HasanJamal96/esp32_prayer_reminder/Code/main/data/bg.jpg

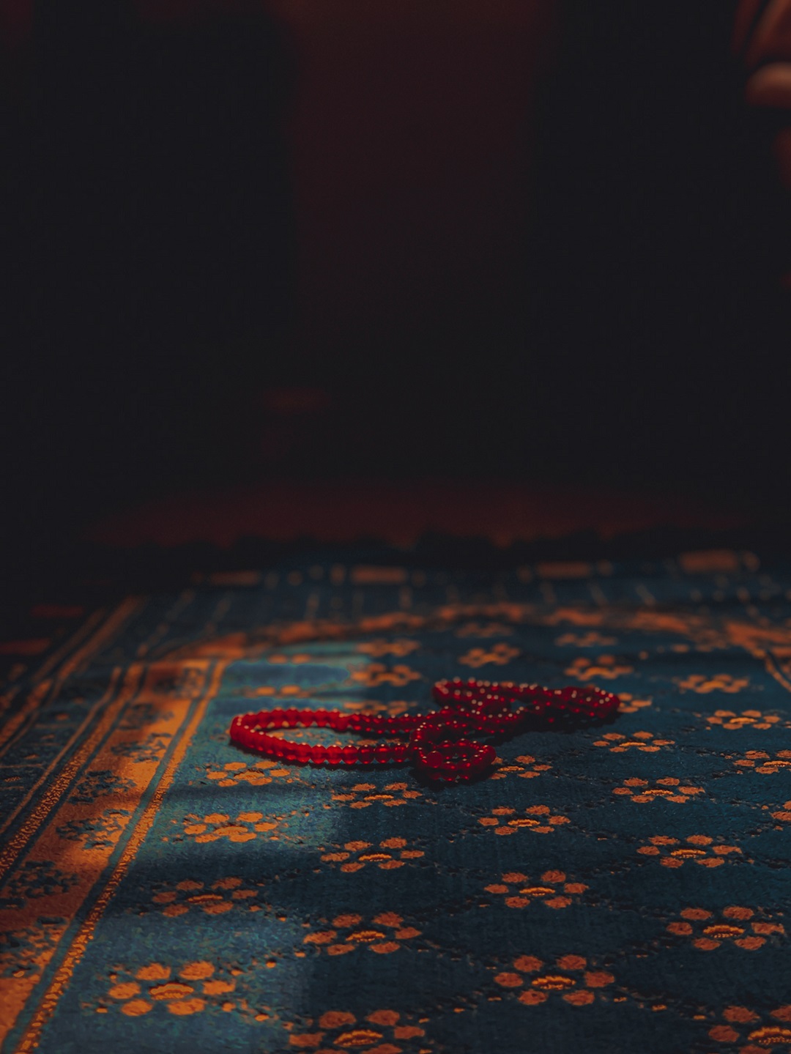
Code/main/data/bg.jpg
