HasanJamal96/esp32_prayer_reminder/Code/main/WAVFileReader.h

#pragma once

#include "WAVFile.h"
#include <stdio.h>

class WAVFileReader {
  private:
    wav_header_t m_wav_header;
    FILE *m_fp;

  public:
    WAVFileReader(FILE *fp);
    int sample_rate() { return m_wav_header.sample_rate; }
    int read(int16_t *samples, int count);
};
