HasanJamal96/esp32_prayer_reminder/Code/main/button.h

#include <Arduino.h>


class Button{
  public:
    Button(uint8_t pin, uint32_t dbTime=25)
        : m_pin(pin), m_dbTime(dbTime){}

    void begin();
    bool read();
    bool pressedFor(uint32_t ms);

  private:
    uint8_t m_pin;          // arduino pin number connected to button
    uint32_t m_dbTime;      // debounce time (ms)
    bool m_state;           // current button state, true=pressed
    bool m_lastState;       // previous button state
    bool m_changed;         // state changed since last read
    uint32_t m_time;        // time of current state (ms from millis)
    uint32_t m_lastChange;
    uint32_t m_pressed_at;
    uint32_t m_released_at;
    uint32_t m_pressed_for;
};
